osmocom/openpcd/hardware/RFID-READER_Bm115_1.pdf

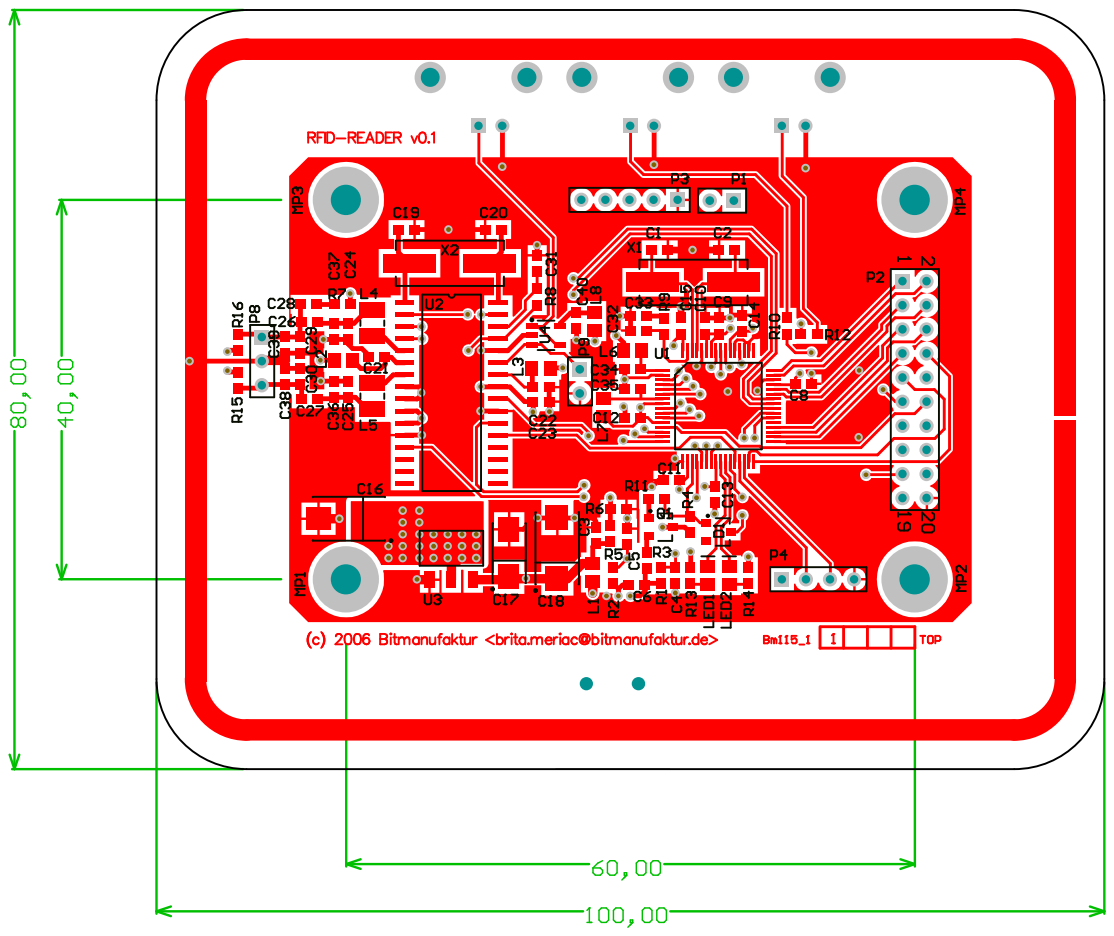
[picture p21: page 1]

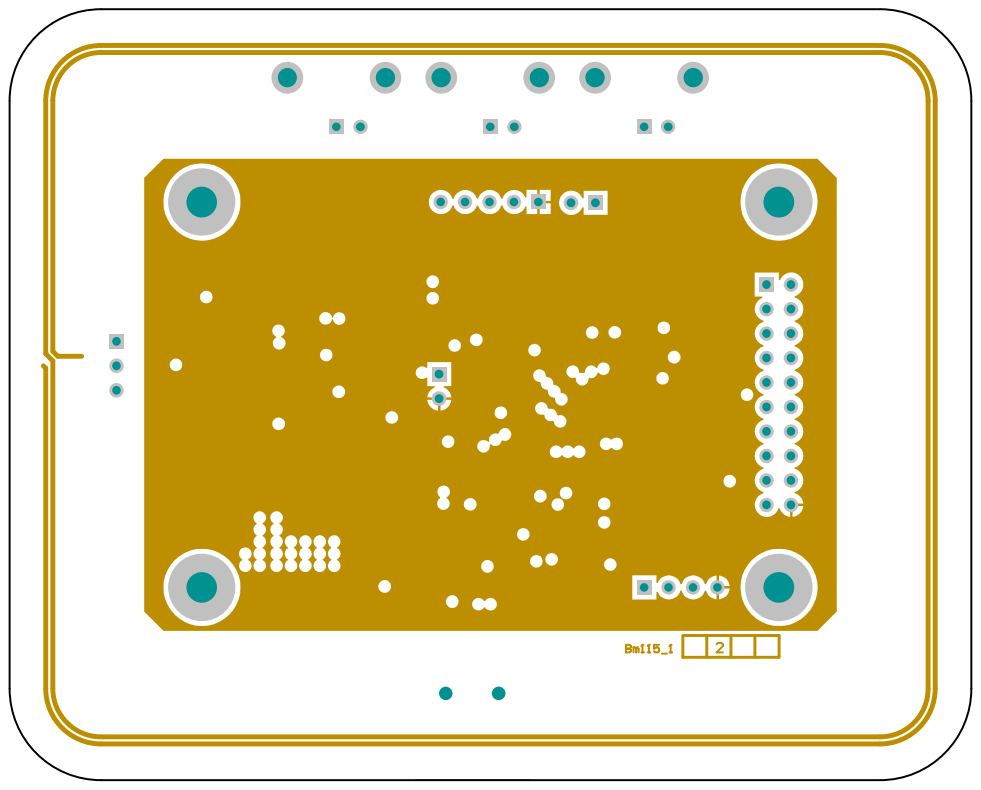
[picture p22: page 2]

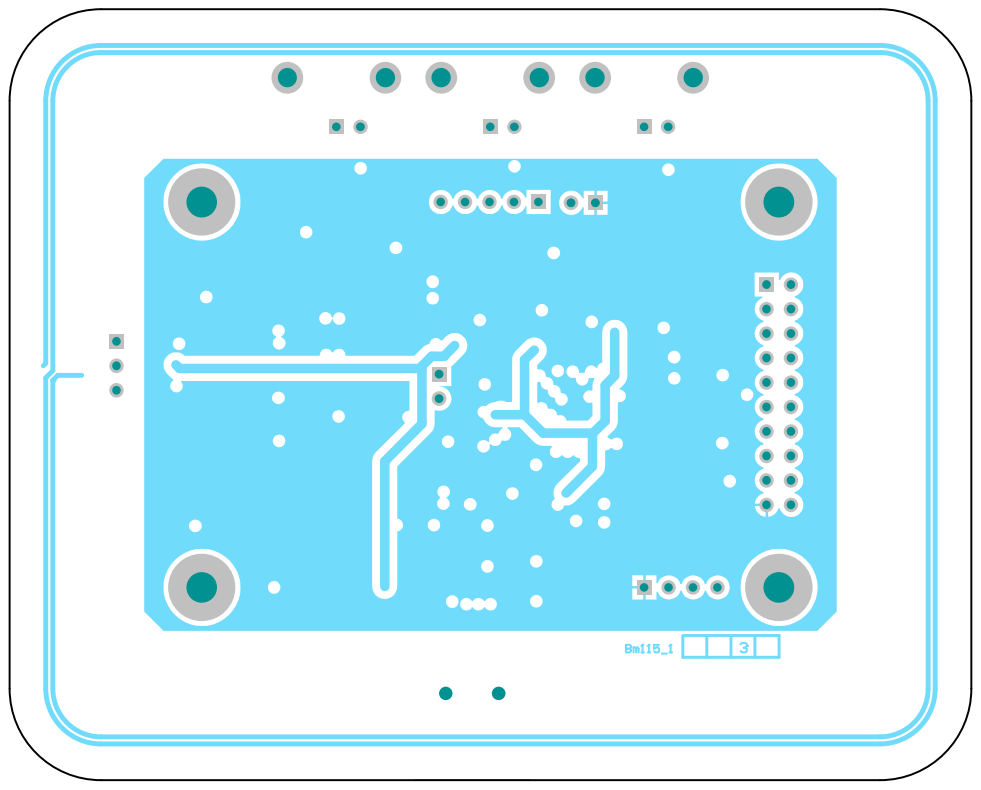
[picture p23: page 3]

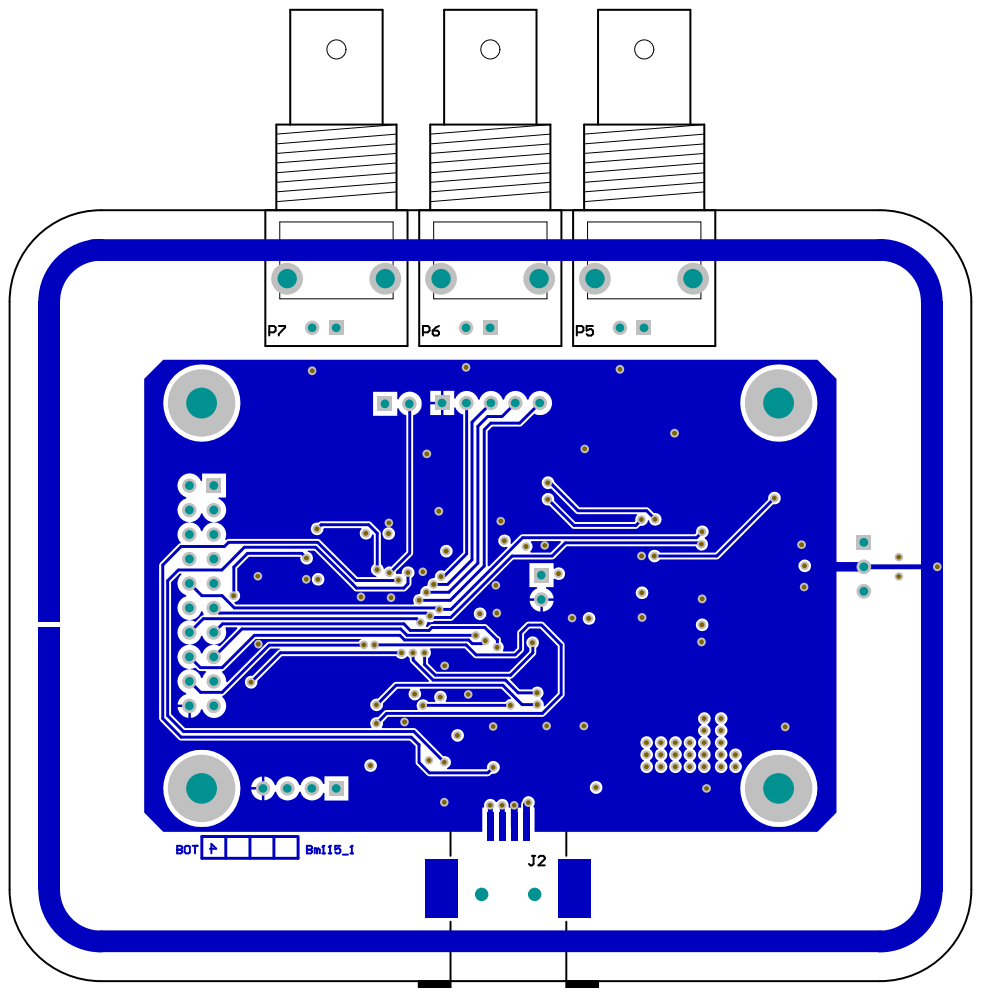
[picture p24: page 4]

Date:; Sheet of File:; H:\Projekte\..\TOP.SchDoc; Drawn By; 1 - TOP

Title
Testboard RFID Reader

http://www.bitmanufaktur.de

Dipl.-Ing. Brita Meriac

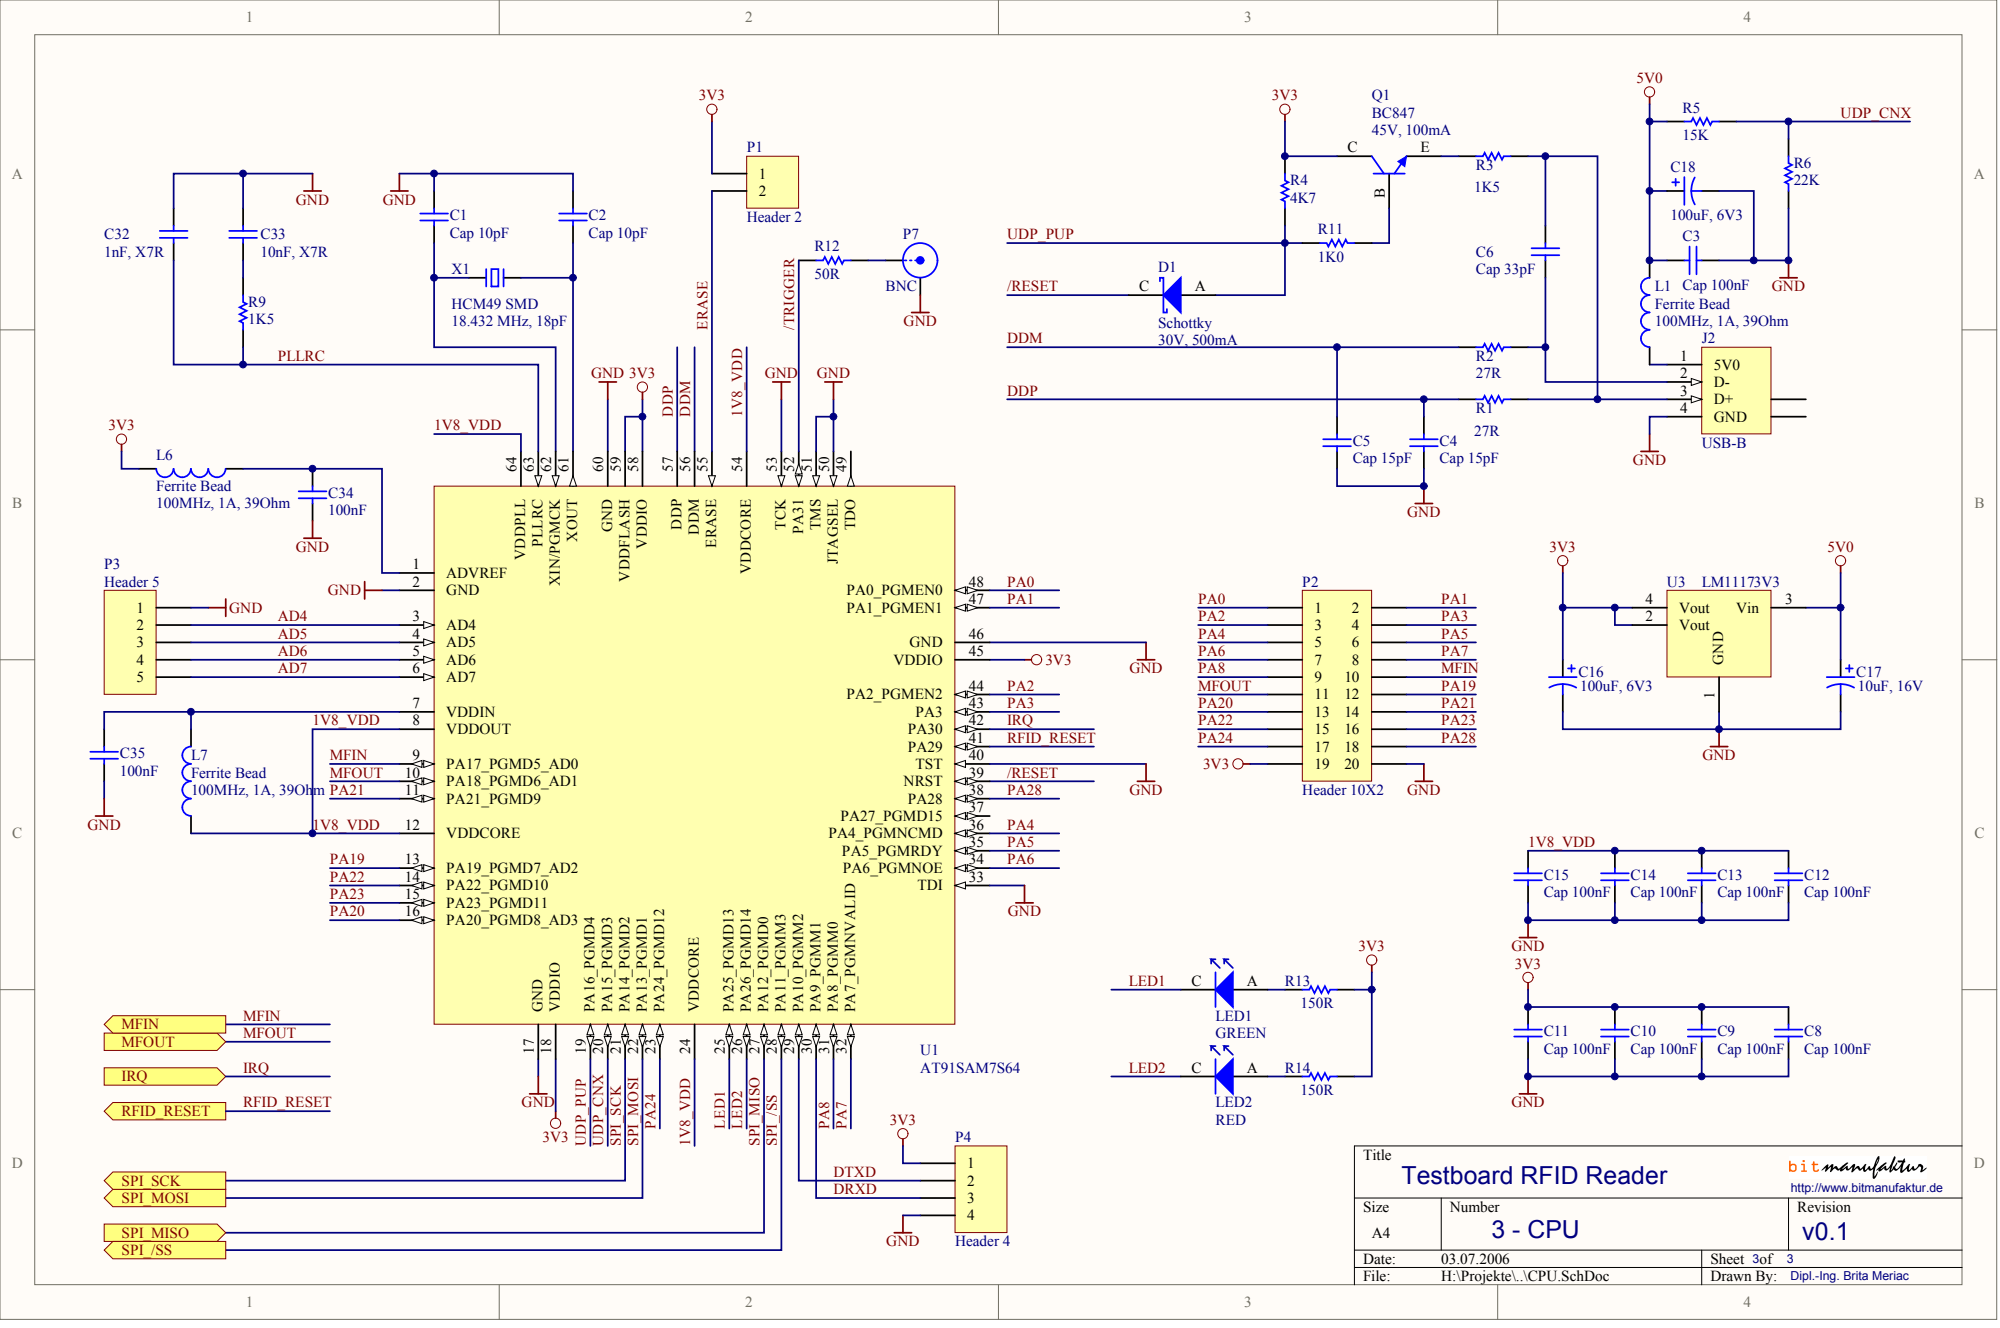
[picture p25: page 6]

18.432 MHz, 18pF 1V8_VDD N01V80VDD N01V80VDD

XOUT 61 XIN/PGMCK 62 PLLRC 63 VDDPLL 64

1V8_VDD N01V80VDD | 8

MF IN N0MFIN MFOUT N0MFOUT N0PA21 1V8_VDD N01V80VDD | 9 | PA18_PGMD6_AD1 10 PA21_PGMD9 11 P0U1011 N0PA21

DTXD N0DTXD N0DTXD
DRXD N0DRXD N0DRXD | P0P402 P0P402

http://www.bitmanufaktur.de

Dipl.-Ing. Brita Meriac

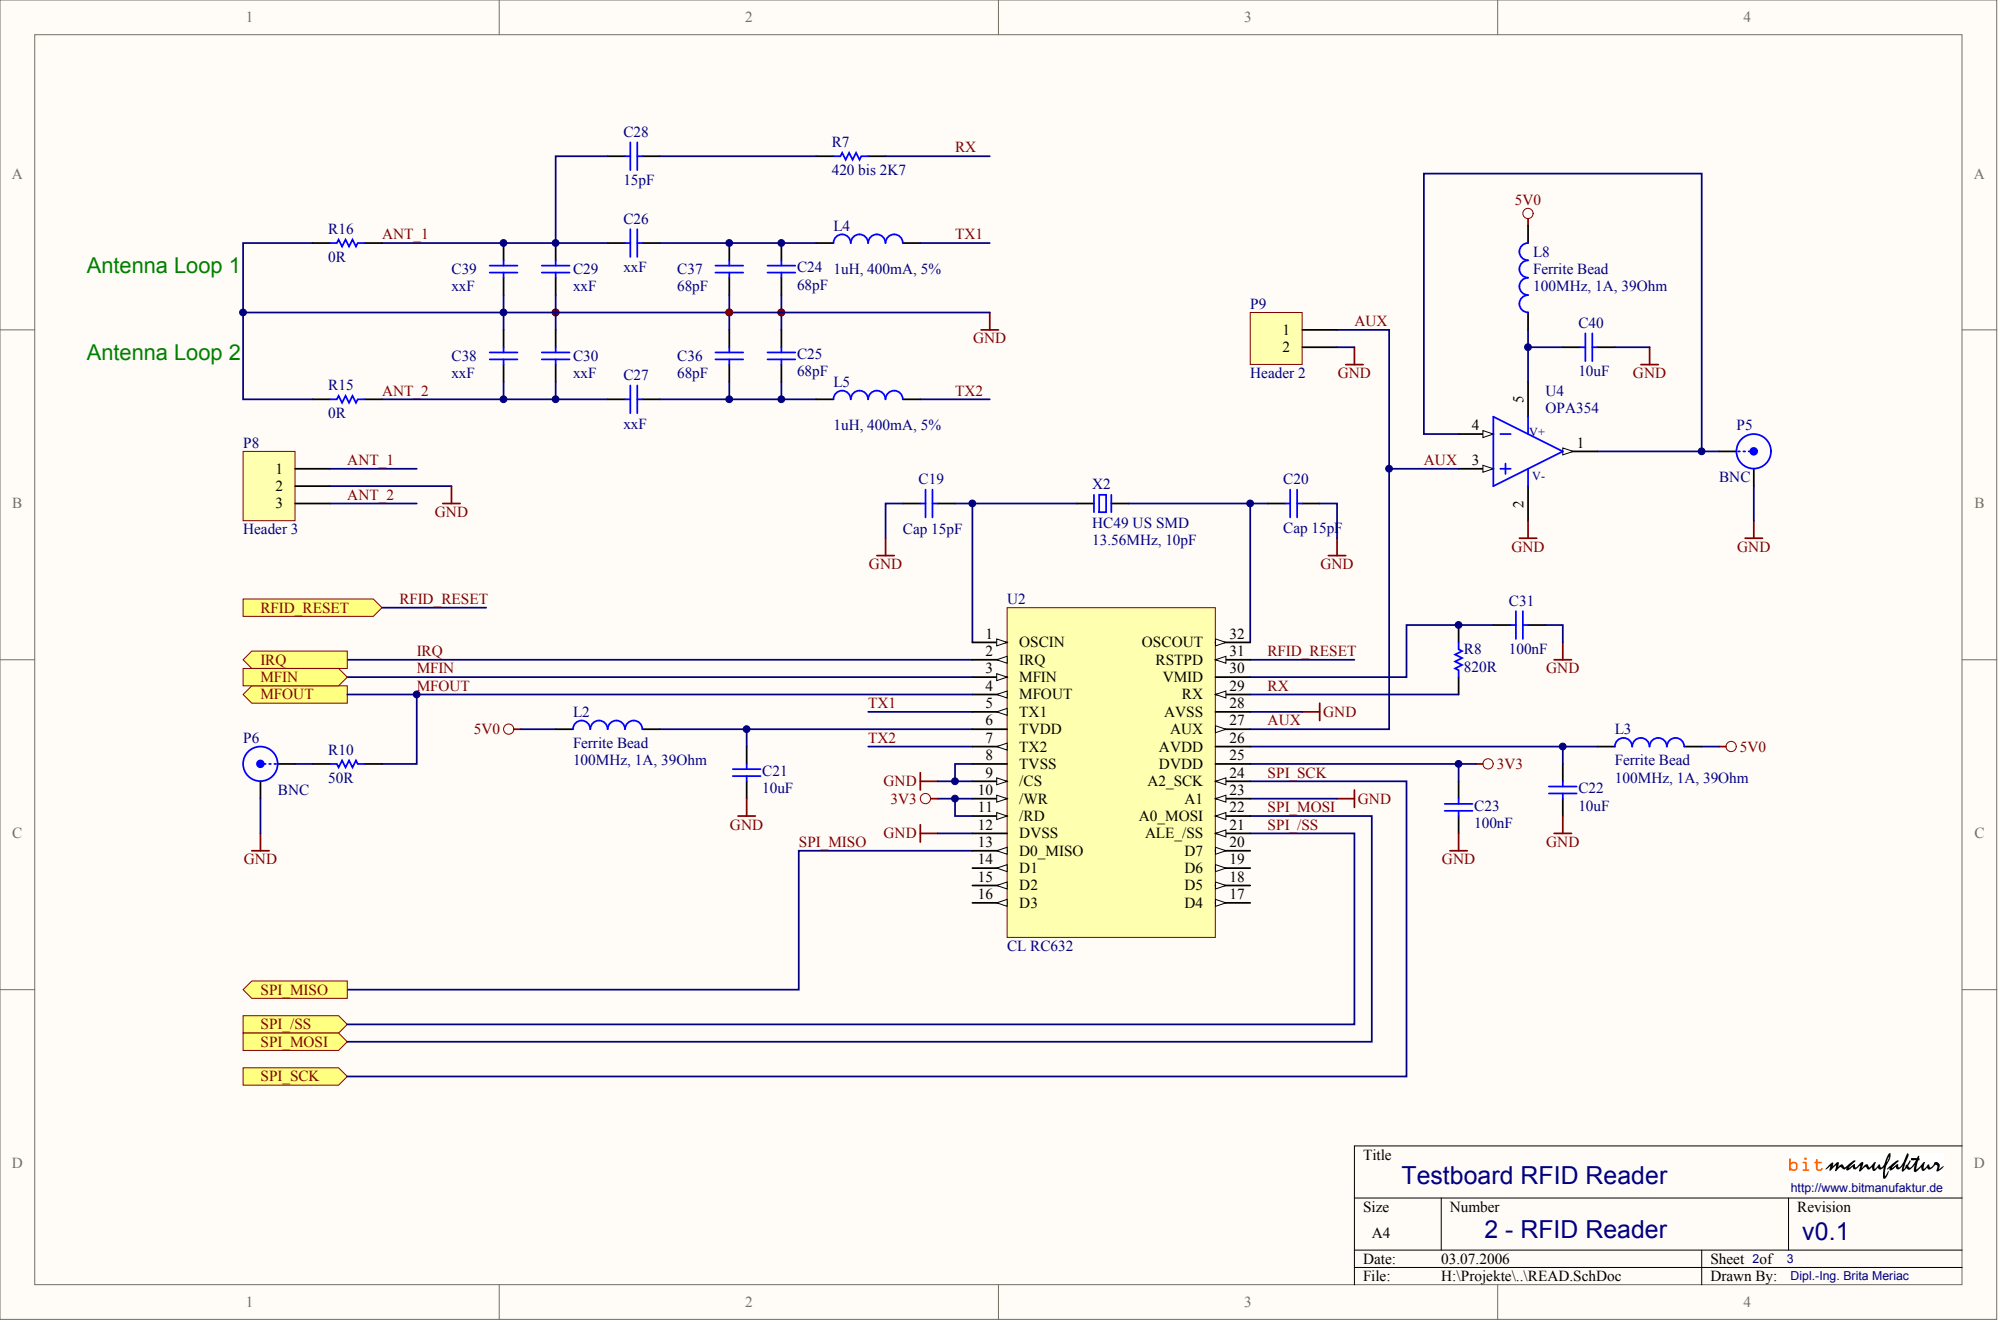
[picture p26: page 7]

RFID_RESET N0RFID0RESET | R8

MFOUT 4 P0U204 N0MFOUT P0U2029 P0U2029 P0U2029 P0U2029 | RX N0RX

TX1 5 P0U2028 P0U2028 P0U2028 P0U2028 TVDD 6 TX2 7 TVSS 8 /CS 9

P0U2010 P0U2010 | /WR 10
/RD 11 | SPI_MOSI
DVSS 12 P0U2021 P0U2021 P0U2021 P0U2021 | SPI_/SS N0SPI0/SS

SPI_MISO | D0_MISO 13 P0U2013 N0SPI0MISO P0U2020 P0U2020 P0U2020 P0U2020 P0U2013 P0U2013 P0U2013

D1 14 P0U2019 P0U2019 P0U2019 P0U2019
D2 15 P0U2018 P0U2018 P0U2018 P0U2018

http://www.bitmanufaktur.de

Dipl.-Ing. Brita Meriac
