osmocom/openpcd/hardware/RFID-READER_SCH01.pdf

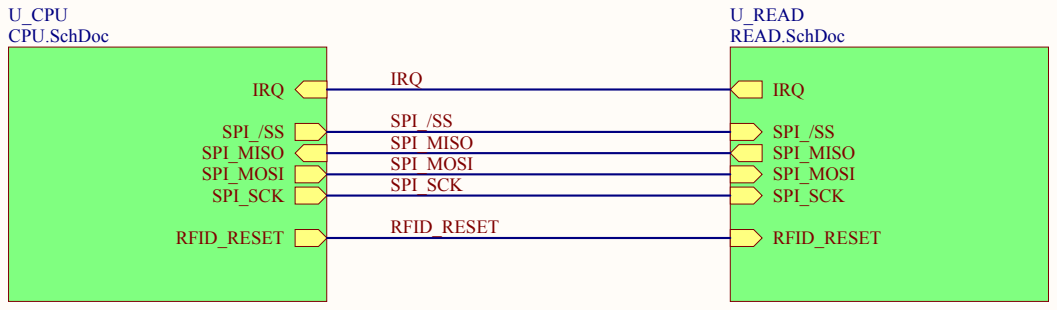
[picture p27: page 1]
Date:; Sheet of; File:; H:\Projekte\..\TOP.SchDoc; Drawn By:; 1 - TOP

Title
Testboard RFID Reader

http://www.bitmanufaktur.de

Dipl.-Ing. Brita Meriac

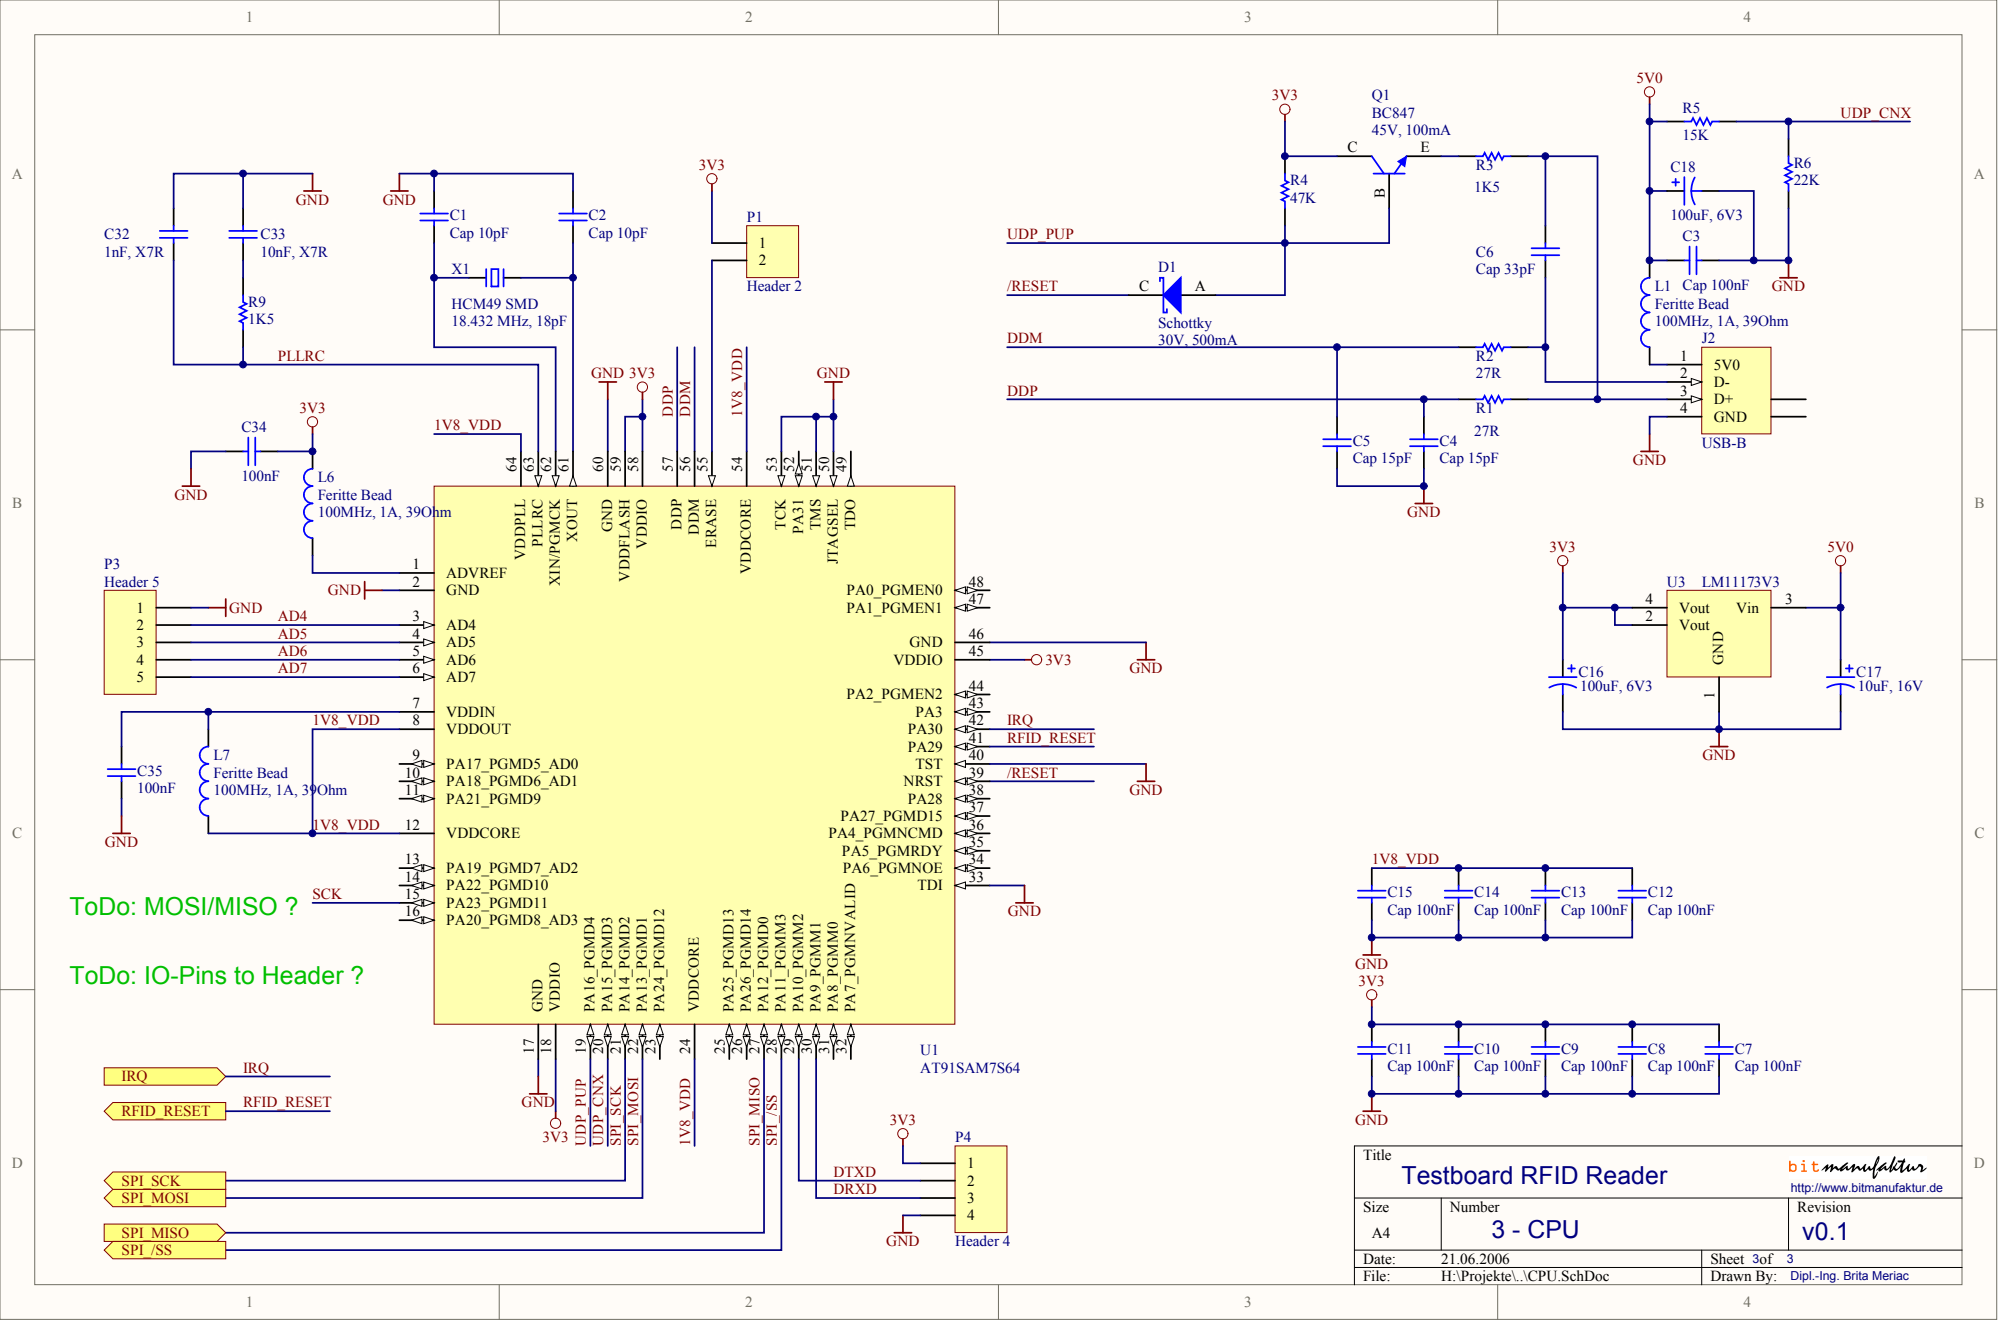
[picture p28: page 2]

18.432 MHz, 18pF 1V8_VDD N01V80VDD N01V80VDD

XOUT 61 XIN/PGMCK 62 PLLRC 63 VDDPLL 64

1V8_VDD N01V80VDD | 8

1V8_VDD N01V80VDD | 9

ToDo: IO-Pins to Header ?

http://www.bitmanufaktur.de

Dipl.-Ing. Brita Meriac

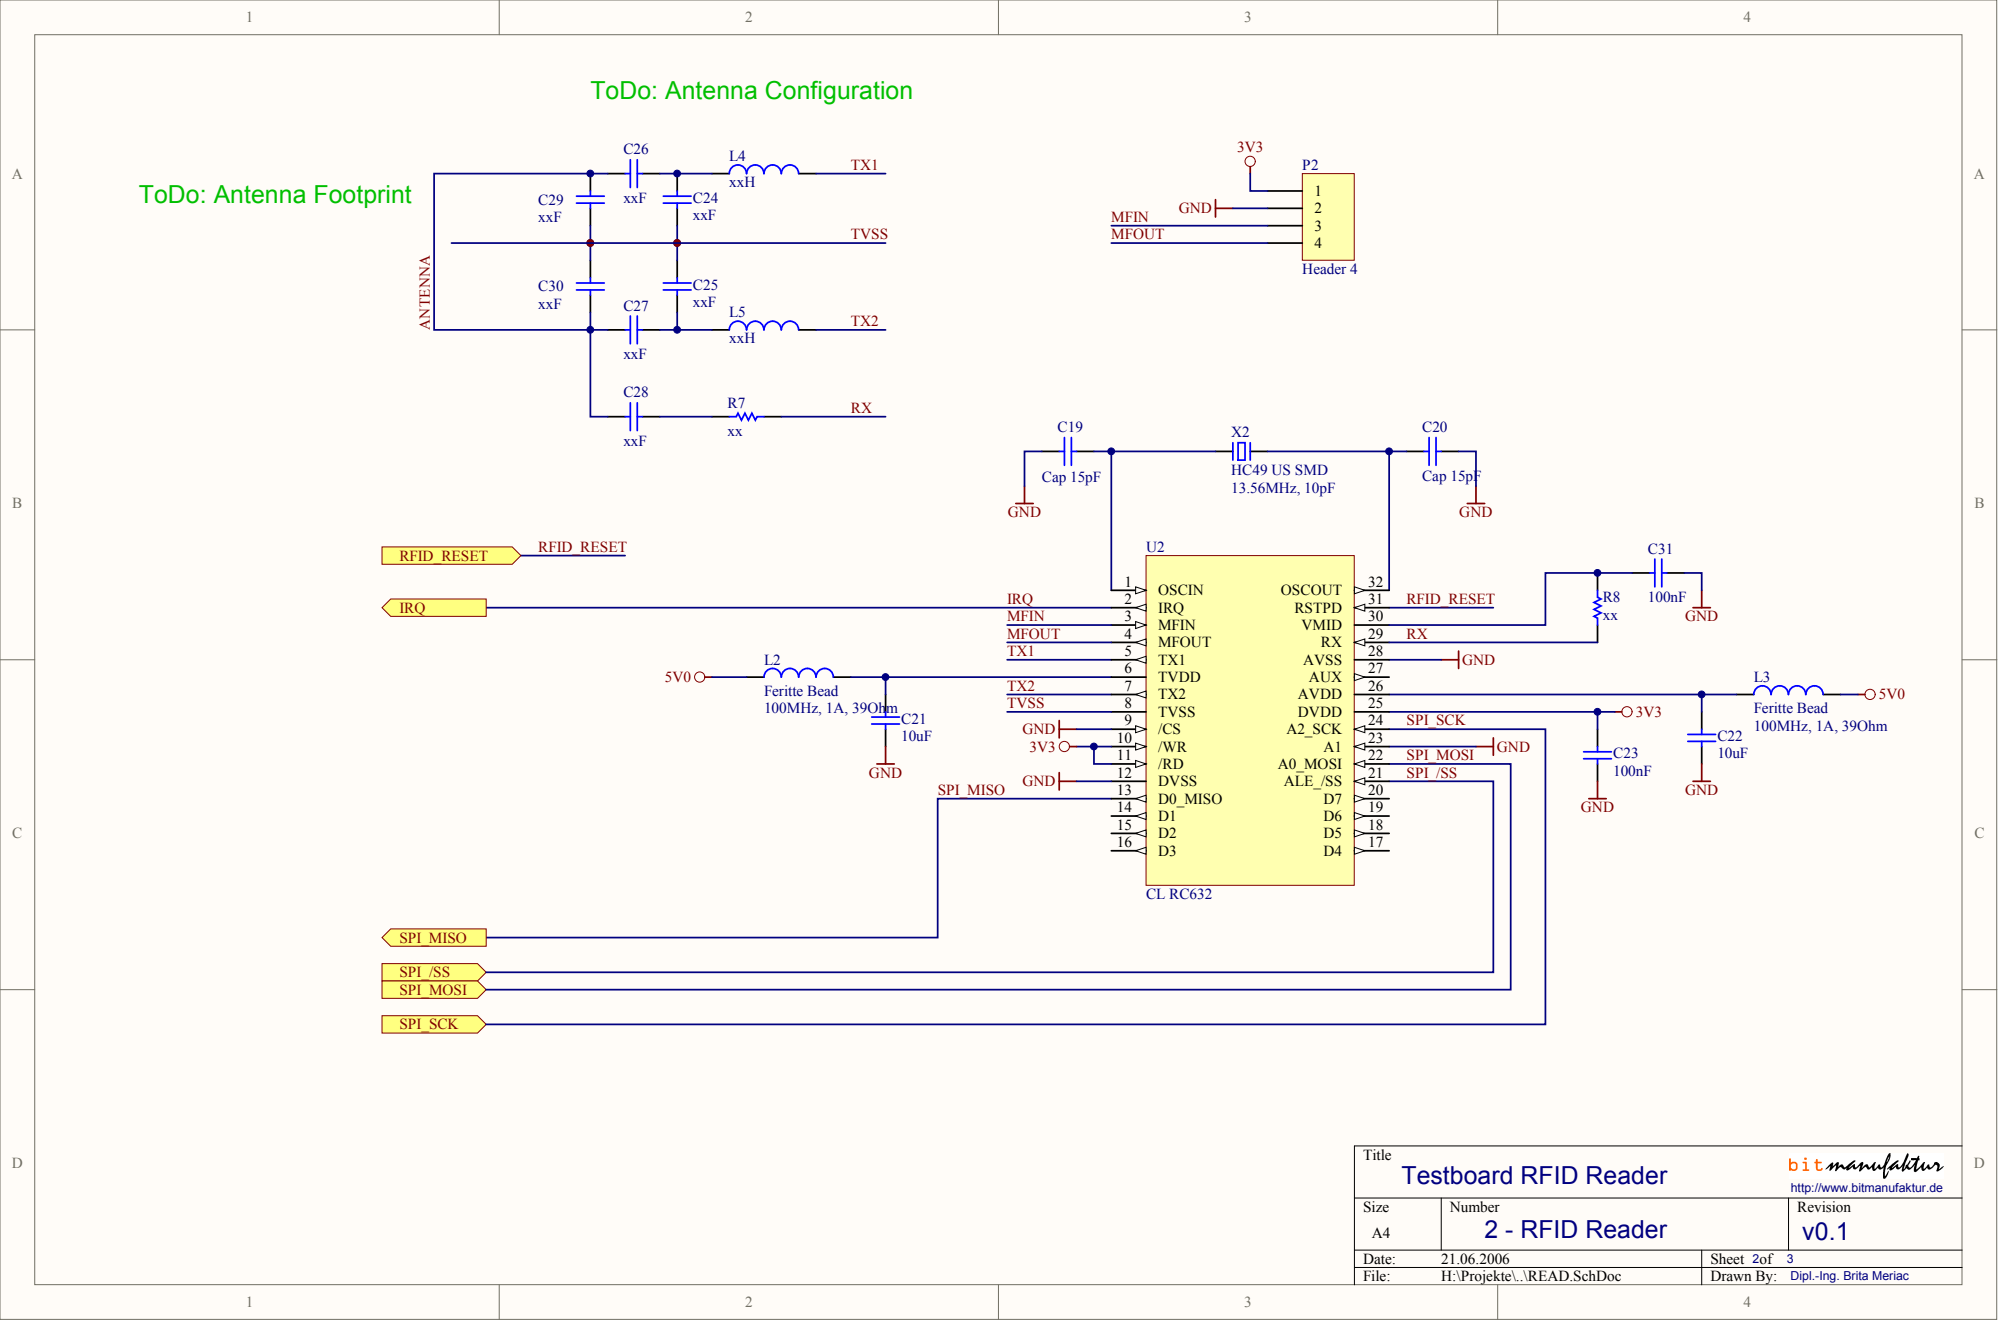
[picture p29: page 3]

P0U2010 P0U2010 | /WR 10 P0U2022 P0U2022 P0U2022
/RD 11 | SPI_MOSI
DVSS 12 P0U2021 P0U2021 P0U2021 P0U2021 | SPI_/SS N0SPI0/SS

SPI_MISO | D0_MISO 13 P0U2013 N0SPI0MISO P0U2020 P0U2020 P0U2020 P0U2020 P0U2013 P0U2013 P0U2013

D1 14 P0U2019 P0U2019 P0U2019 P0U2019
D2 15 P0U2018 P0U2018 P0U2018 P0U2018

http://www.bitmanufaktur.de

Dipl.-Ing. Brita Meriac
