osmocom/openpcd/hardware/v0.4/openpcd_v04-pcb.pdf

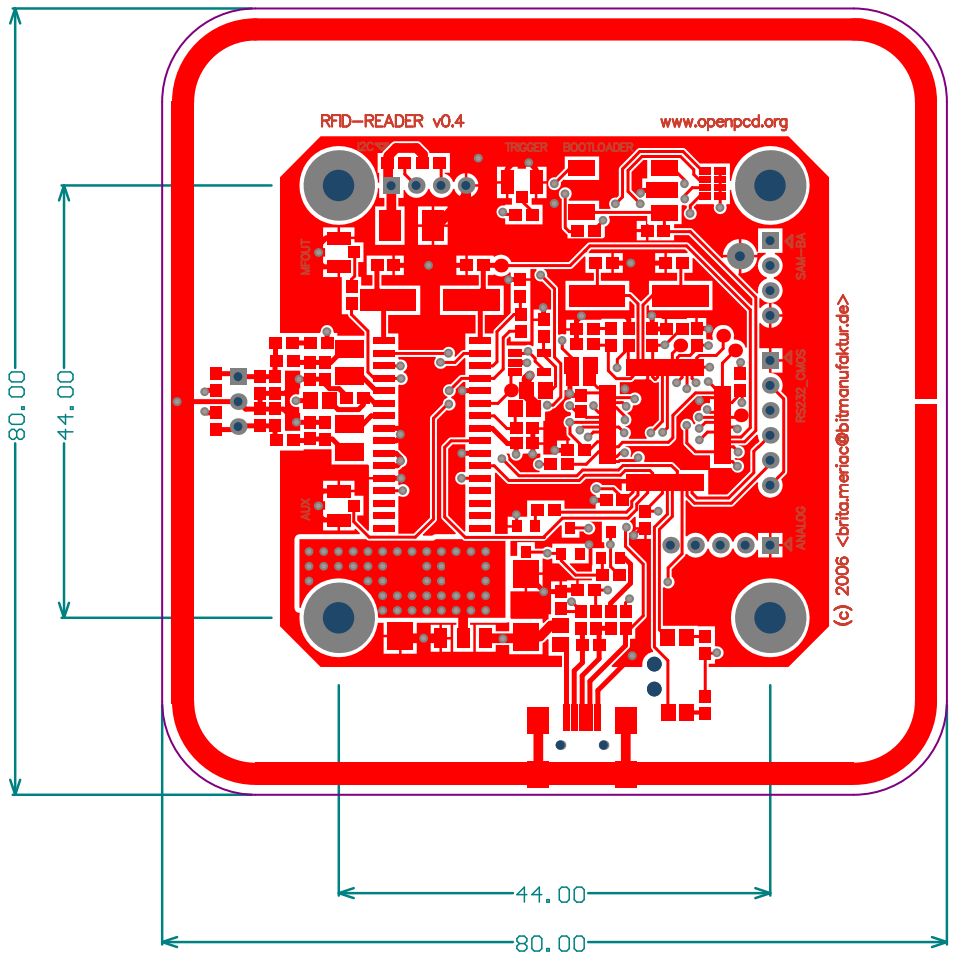
[picture p30: page 1]

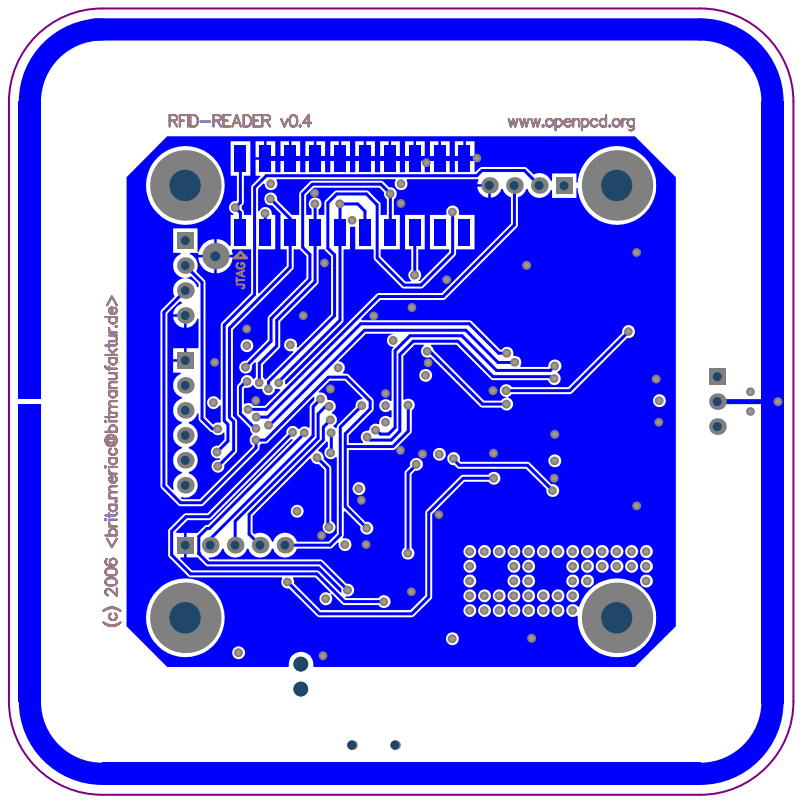
[picture p31: page 2]

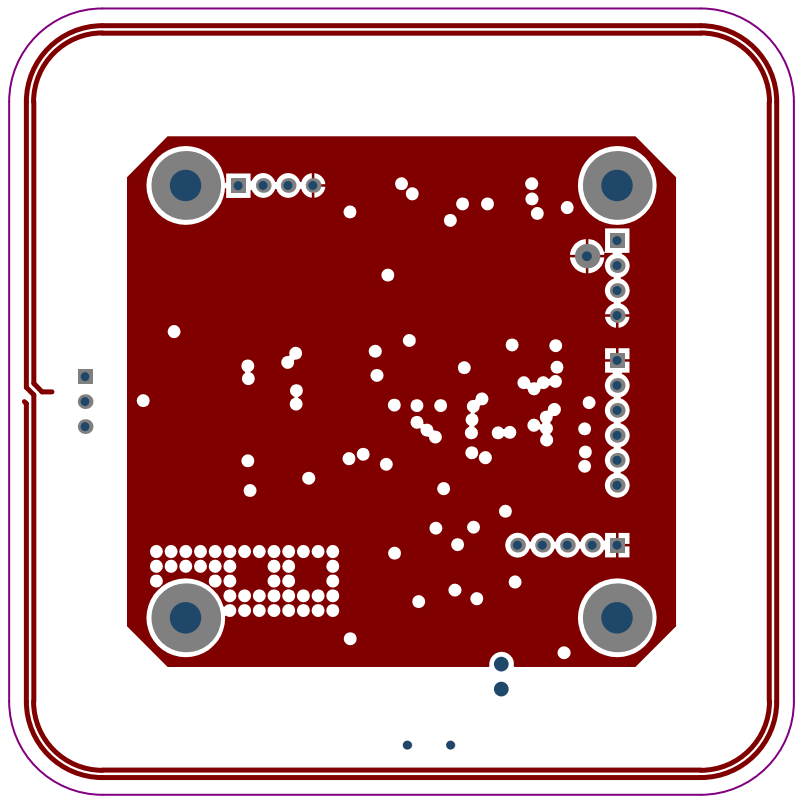
[picture p32: page 3]

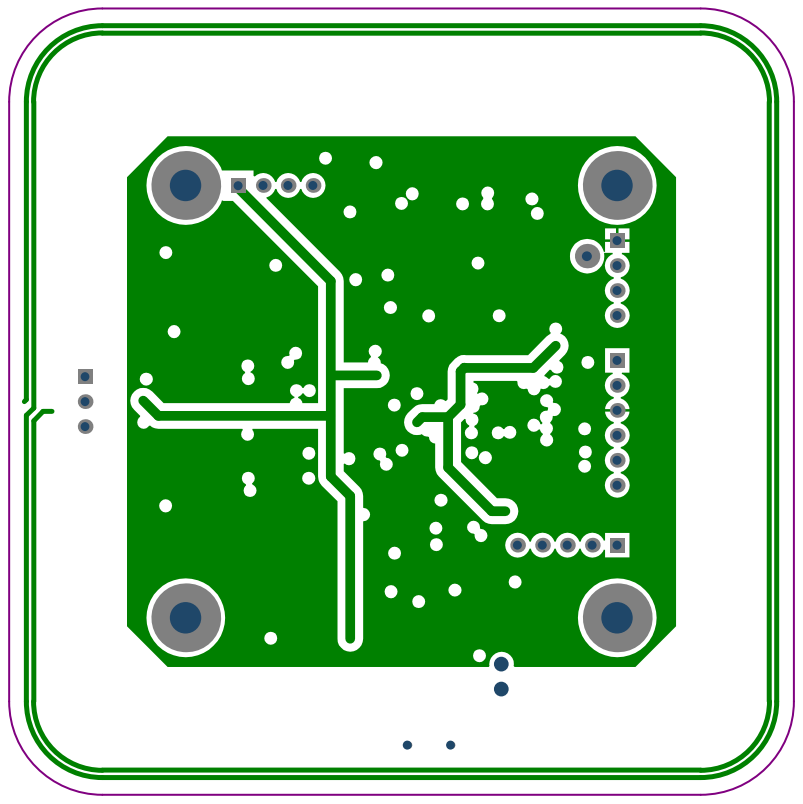
[picture p33: page 4]
