osmocom/openpcd/hardware/v0.4/openpcd_v04-sch.pdf

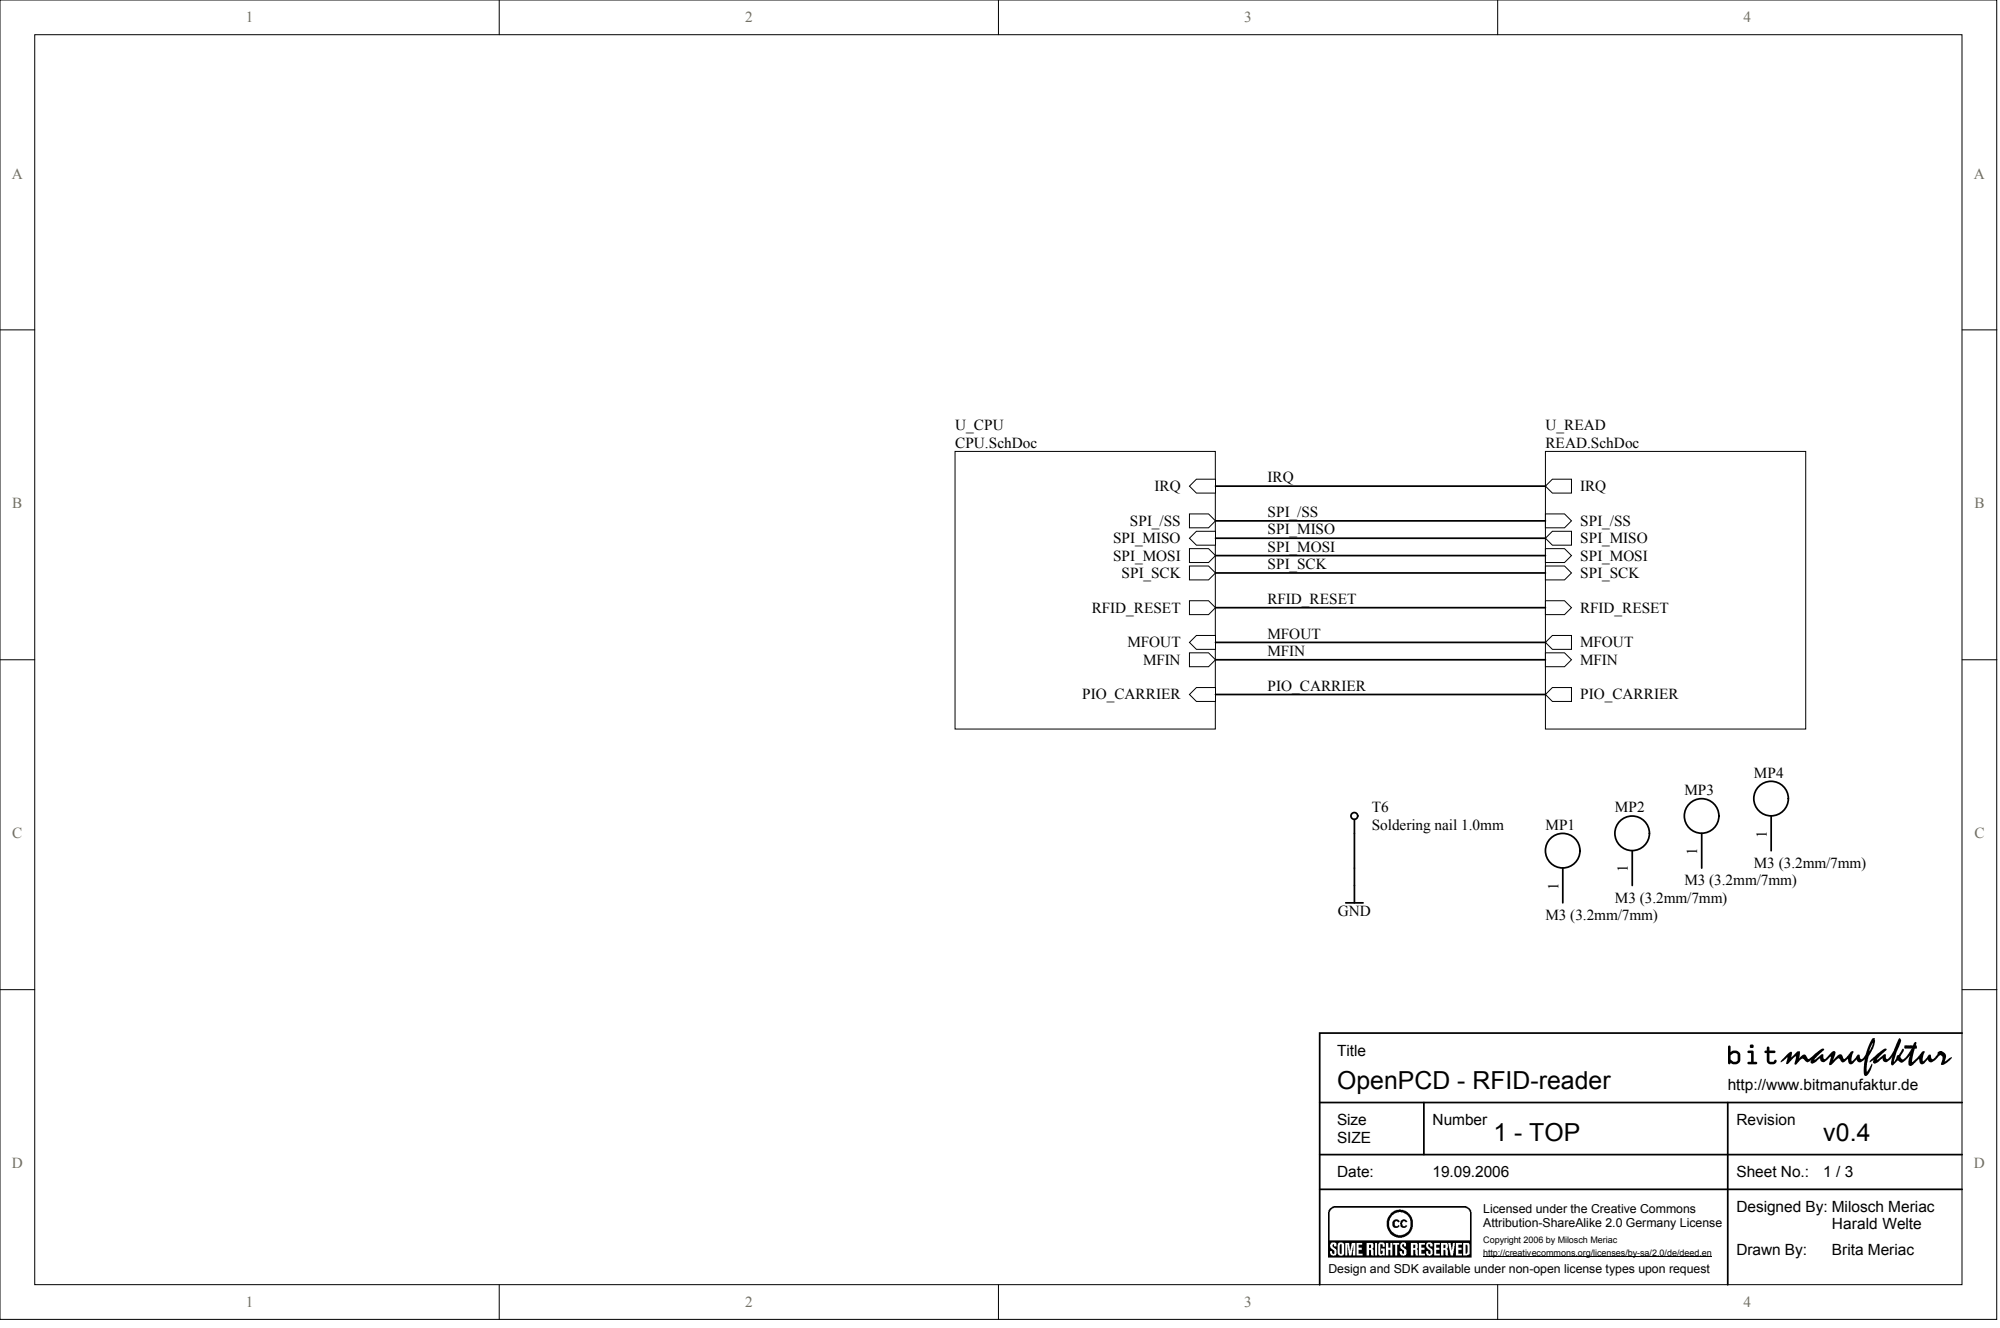
[picture p34: page 1]
Soldering nail 1.0m; Design and SDK available under non-open license types upon request P0MP101

Title
OpenPCD - RFID-reader

ww.bitmanufaktur.de

Siz e SIZE | Number 1 - TOP | Revision v0.4

Date: 19.09.2006 | | Sheet No.: 1 / 3

Licensed under the Creative Commons Attribution-ShareAlike 2.0 Germany License http://creativecommons.org/licenses/by-sa/2.0/de/deed.en Cop yri g ht 2006 b y Mi losch Meriac | | Designed By : Milosch Meriac Harald Welte Drawn By : Brita Meriac

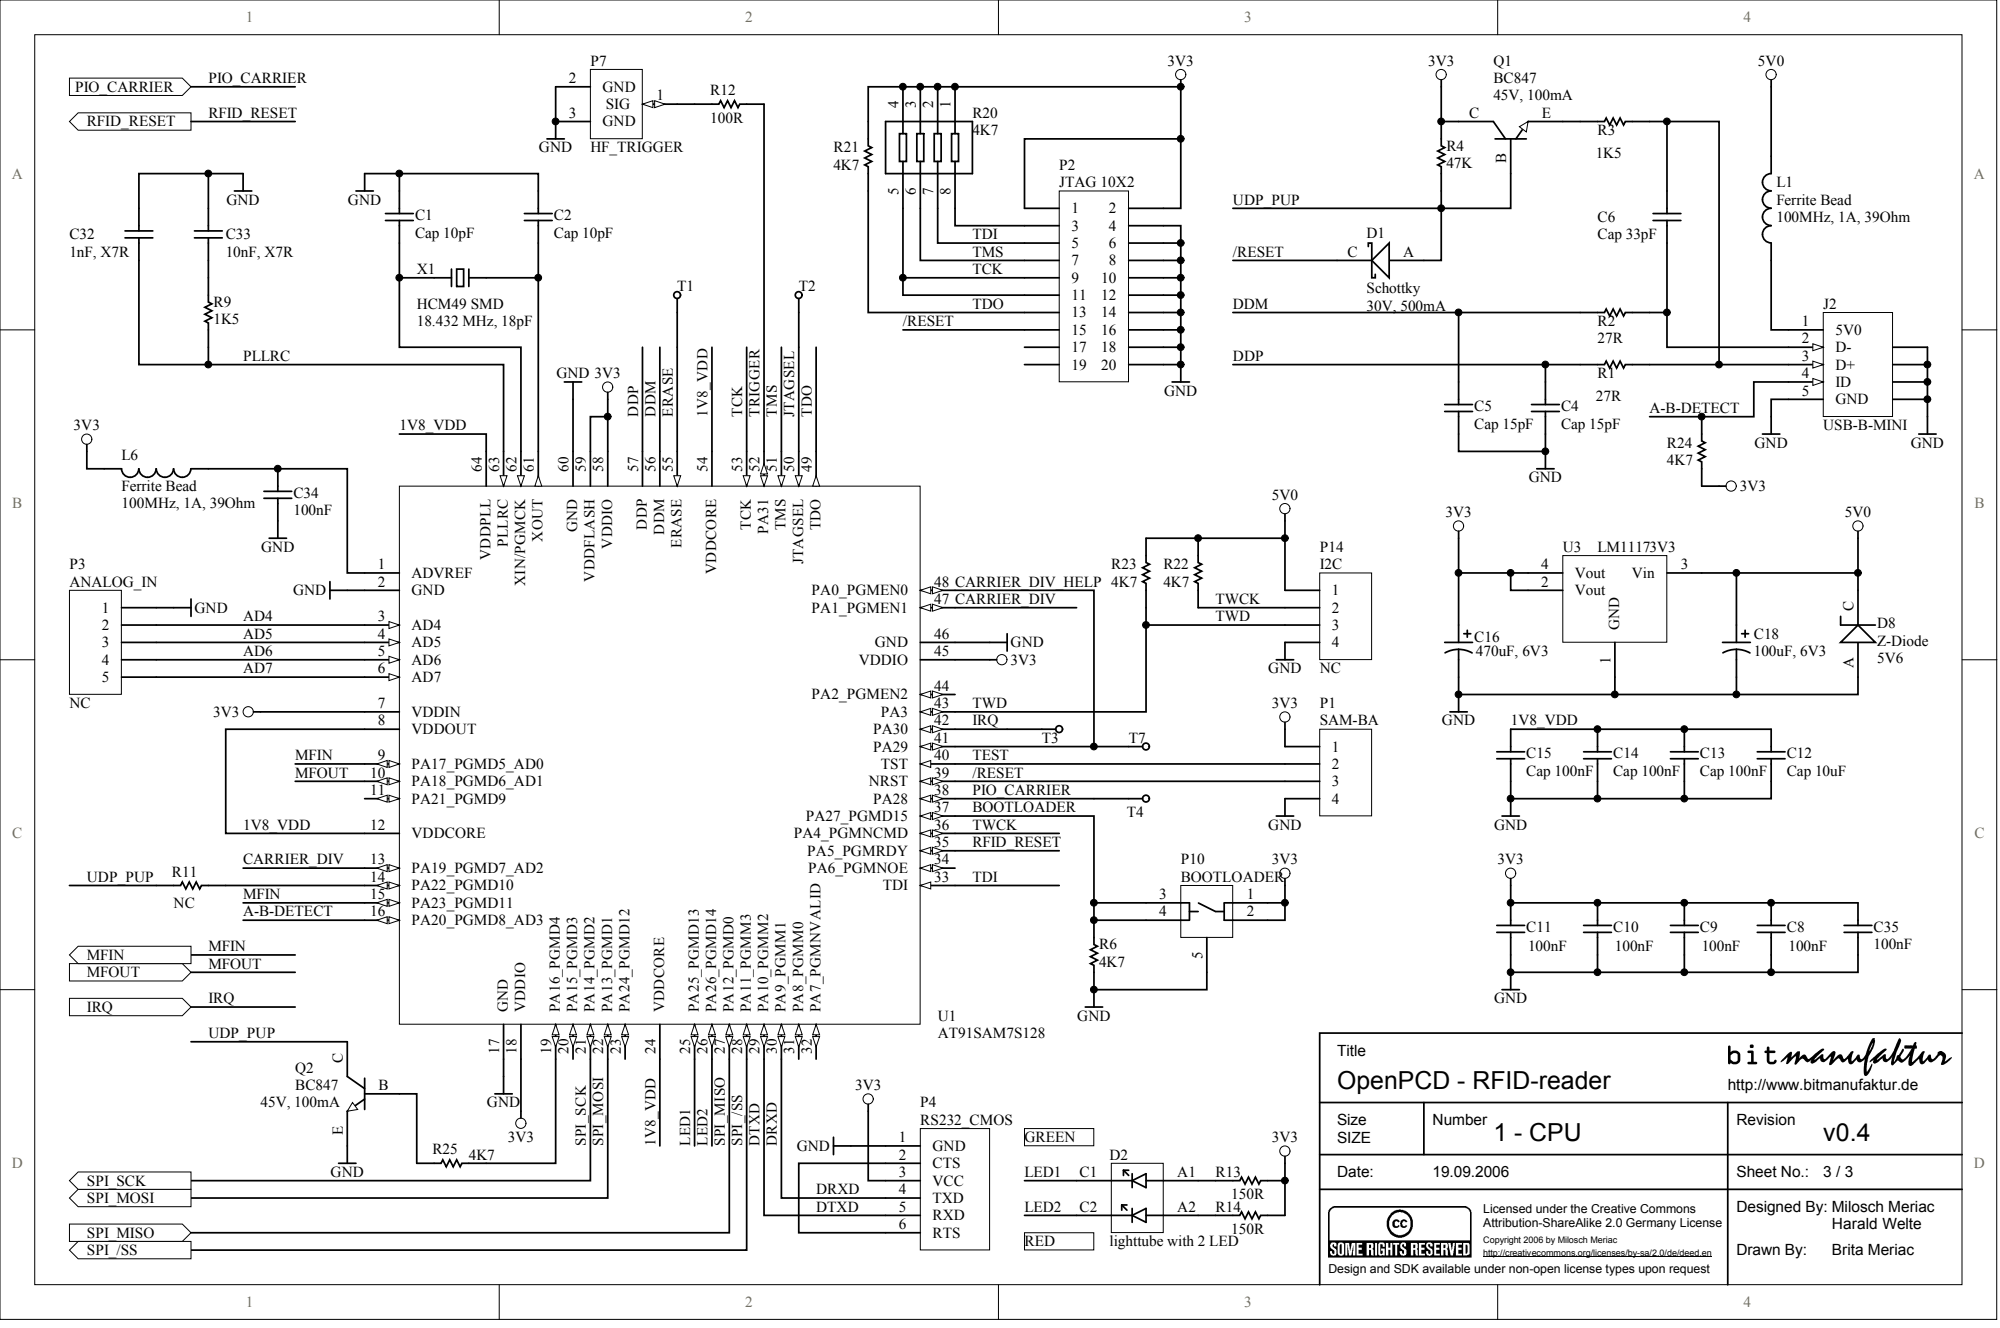
[picture p35: page 2]

XOUT 61 XIN/PGMCK 62 PLLRC 63 VDDPLL 64

Siz e SIZE | Number 1 - CPU | Revision v0.4

4 | | LED1 LED2 C2 N0LED2 | P0R1302 P0R1302 P0R1302 P0R1302 P0R1301 P0R1301 P0R1301 P0R1301 A2 R14 P0D20A2 P0D20A2 P0D20A2 P0D20A2

Date: 19.09.2006 | | Sheet No.: 3 / 3

DTXD N0DTXD | 5

Licensed under the Creative Commons Attribution-ShareAlike 2.0 Germany License http://creativecommons.org/licenses/by-sa/2.0/de/deed.en Cop yri g ht 2006 b y Mi losch Meriac Design and SDK available under non-open license types upon request | | Designed By : Milosch Meriac Harald Welte Drawn By : Brita Meriac

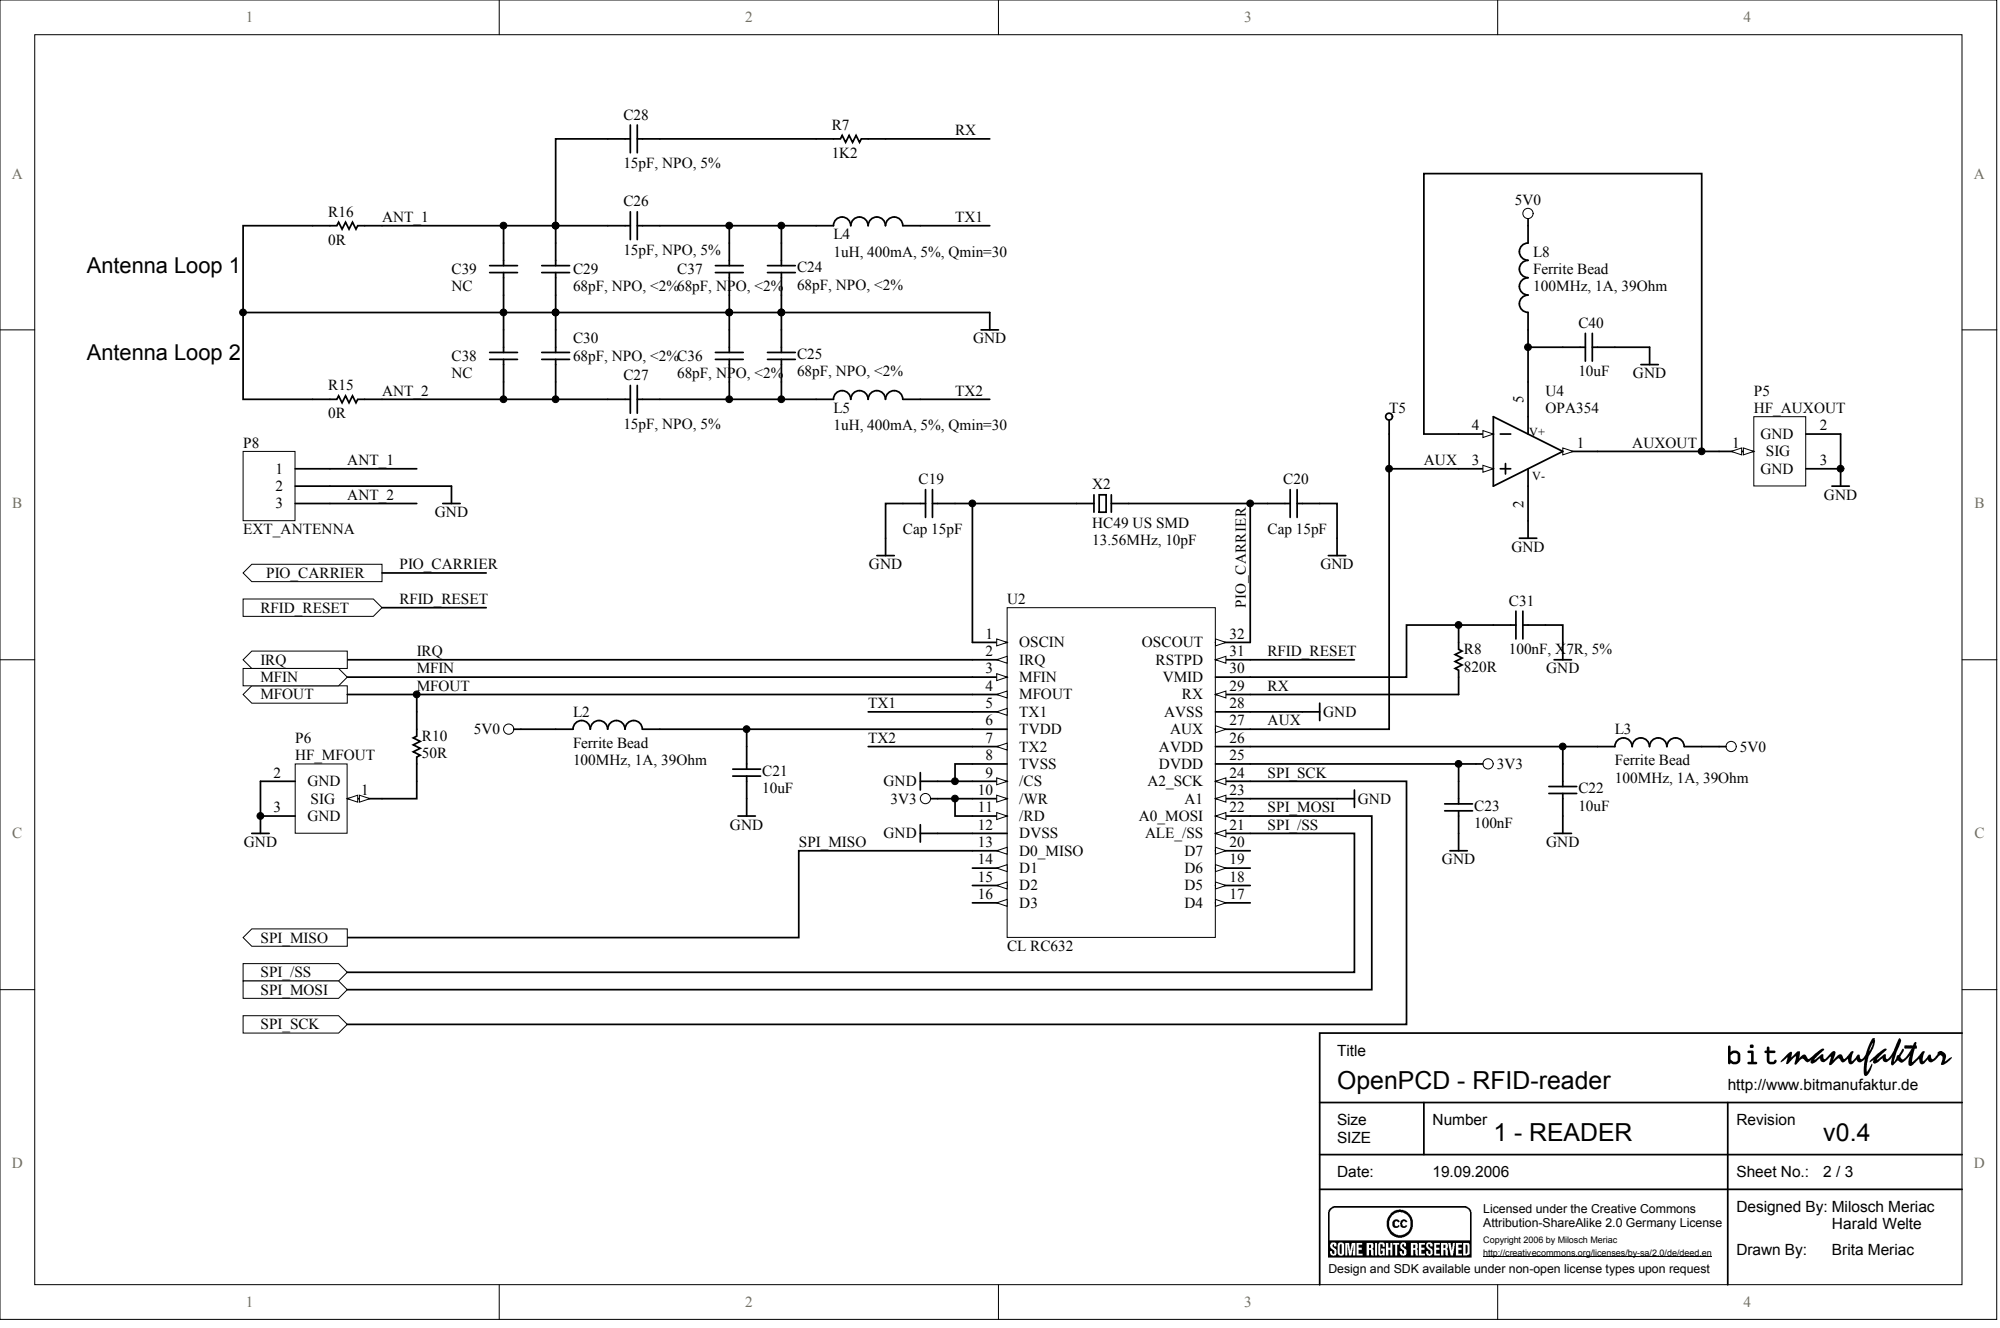
[picture p36: page 3]

RF ID_RESET N0RFID0RESET | R8

P0U204 N0MFOUT P0U2029 P0U2029 P0U2029 P0U2029 | | RX N0RX

3 | P0P601 P0P601 | 1 GND | | P0U2010 P0U2010 | /WR 10

/RD 11 | SP I_MOSI
DVSS 12 P0U2021 P0U2021 P0U2021 P0U2021 | SP I_/SS N0SPI0/SS

SP I_MISO | D0_MISO 13 P0U2013 N0SPI0MISO P0U2020 P0U2020 P0U2020 P0U2020 P0U2013 P0U2013 P0U2013

D1 14 P0U2019 P0U2019 P0U2019 P0U2019
D2 15 P0U2018 P0U2018 P0U2018 P0U2018

Siz e SIZE | Number 1 - READER | Revision v0.4

Date: 19.09.2006 | | Sheet No.: 2 / 3

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
