osmocom/openpcd/hardware/v0.4/openpcd_v04_place.pdf

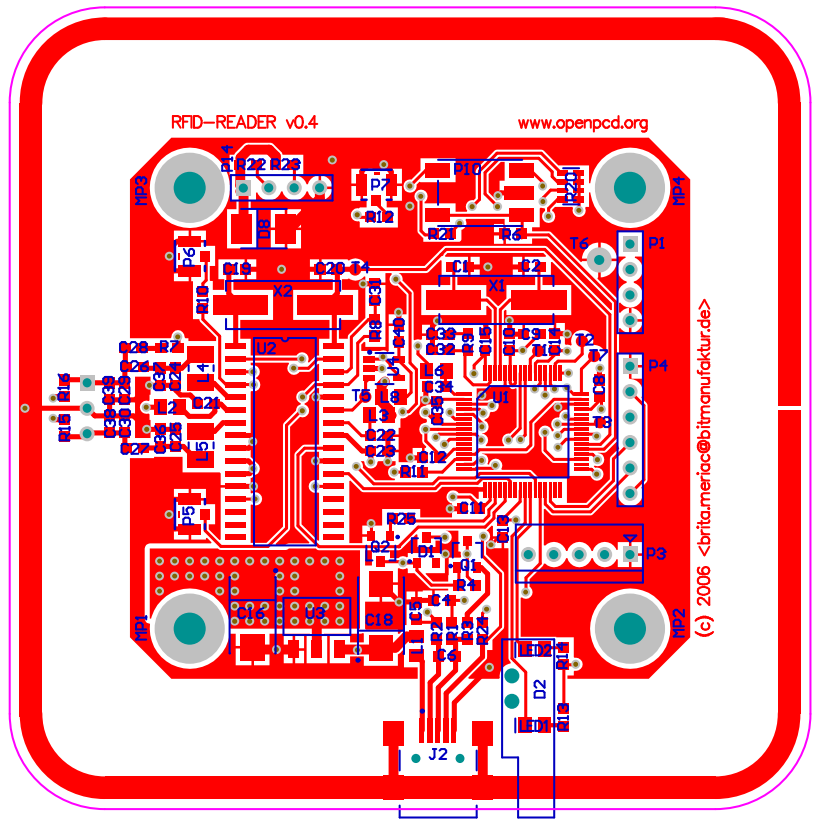
[picture p37: page 1]
