osmocom/openpcd/openpicc/application/ssc.c

/* AT91SAM7 SSC controller routines for OpenPICC
 * (C) 2006 by Harald Welte <hwelte@hmw-consulting.de>
 * (C) 2007-2008 Henryk Plötz <henryk@ploetzli.ch>
 *
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
 * We use SSC for both TX and RX side.
 *
 * RX side is interconnected with demodulated carrier 
 *
 * TX side is interconnected with load modulation circuitry
 */

#include <FreeRTOS.h>
#include <queue.h>
#include <task.h>
#include <openpicc.h>

#include <string.h>
#include <errno.h>

#include "ssc.h"
#include "iso14443.h"

#include "clock_switch.h"
#include "tc_cdiv_sync.h"
#include "tc_fdt.h"
#include "led.h"

#include "usb_print.h"
#include "cmd.h"

#define PRINT_DEBUG 0
#define DEBUG_DATA_GATING 0

struct _ssc_handle {
	enum ssc_mode mode;
	const struct openpicc_hardware *openpicc;
	ssc_dma_rx_buffer_t* rx_buffer[2];
	ssc_dma_tx_buffer_t* tx_buffer;
	ssc_callback_t callback;
	xQueueHandle rx_queue;
	AT91PS_PDC pdc;
	AT91PS_SSC ssc;
	u_int8_t rx_enabled, tx_enabled;
	u_int8_t rx_running, tx_running, tx_need_switching;
};

static ssc_handle_t _ssc;
static const ssc_mode_def ssc_modes[] = {
	/* Undefined, no size set */
	[SSC_MODE_NONE]		   = {SSC_MODE_NONE, 0, 0, 0},
	/* 14443A Frame */
	[SSC_MODE_14443A]      = {SSC_MODE_14443A, 
		ISO14443_BITS_PER_SSC_TRANSFER * ISO14443A_SAMPLE_LEN,               // transfersize_ssc 
		ISO14443_BITS_PER_SSC_TRANSFER * ISO14443A_SAMPLE_LEN <= 8 ? 8 : 16, // transfersize_pdc 
		DIV_ROUND_UP(ISO14443A_MAX_RX_FRAME_SIZE_IN_BITS, ISO14443_BITS_PER_SSC_TRANSFER) },
};
static struct {
	ssc_metric metric;
	char *name;
	int value;
} ssc_metrics[] = {
		[METRIC_RX_OVERFLOWS]      = {METRIC_RX_OVERFLOWS, "Rx overflows", 0},
		[METRIC_FREE_RX_BUFFERS]   = {METRIC_FREE_RX_BUFFERS, "Free Rx buffers", 0},
		[METRIC_MANAGEMENT_ERRORS] = {METRIC_MANAGEMENT_ERRORS, "Internal buffer management error", 0},
		[METRIC_MANAGEMENT_ERRORS_1] = {METRIC_MANAGEMENT_ERRORS_1, "Internal buffer management error type 1", 0},
		[METRIC_MANAGEMENT_ERRORS_2] = {METRIC_MANAGEMENT_ERRORS_2, "Internal buffer management error type 2", 0},
		[METRIC_MANAGEMENT_ERRORS_3] = {METRIC_MANAGEMENT_ERRORS_3, "Internal buffer management error type 3", 0},
		[METRIC_LATE_TX_FRAMES]    = {METRIC_LATE_TX_FRAMES, "Late Tx frames", 0},
		[METRIC_RX_FRAMES]         = {METRIC_RX_FRAMES, "Rx frames", 0},
		[METRIC_TX_FRAMES]         = {METRIC_TX_FRAMES, "Tx frames", 0},
		[METRIC_TX_ABORTED_FRAMES] = {METRIC_TX_ABORTED_FRAMES, "Aborted Tx frames", 0},
};

static ssc_dma_rx_buffer_t _rx_buffers[SSC_DMA_BUFFER_COUNT];
ssc_dma_tx_buffer_t        _tx_buffer;

/******* PRIVATE "meat" code *************************************************/

#define SSC_RX_IRQ_MASK	(AT91C_SSC_RXRDY | 	\
			 AT91C_SSC_OVRUN | 	\
			 AT91C_SSC_ENDRX |	\
			 AT91C_SSC_RXBUFF |	\
			 AT91C_SSC_RXSYN |	\
			 AT91C_SSC_CP0 |	\
			 AT91C_SSC_CP1)

#define SSC_TX_IRQ_MASK (AT91C_SSC_TXRDY |	\
			 AT91C_SSC_TXEMPTY | 	\
			 AT91C_SSC_ENDTX |	\
			 AT91C_SSC_TXBUFE |	\
			 AT91C_SSC_TXSYN)

static __ramfunc ssc_dma_rx_buffer_t* _unload_rx(ssc_handle_t *sh);
static __ramfunc int _reload_rx(ssc_handle_t *sh);


static int __ramfunc _ssc_rx_irq(u_int32_t orig_sr, int start_asserted, portBASE_TYPE task_woken)
{
	int end_asserted = 0;
	ssc_handle_t *sh = &_ssc;
	u_int32_t orig_rcmr = sh->ssc->SSC_RCMR;
	
#if PRINT_DEBUG
	int old = usb_print_set_default_flush(0);  // DEBUG OUTPUT
	DumpStringToUSB("orig:");  // DEBUG OUTPUT
	DumpUIntToUSB(orig_sr);  // DEBUG OUTPUT
	DumpStringToUSB("\n\r");  // DEBUG OUTPUT
#endif
	u_int32_t sr = orig_sr | _ssc.ssc->SSC_SR;
	
	if( (sr & AT91C_SSC_RXSYN) || start_asserted) {
		sh->ssc->SSC_RCMR = (orig_rcmr & (~AT91C_SSC_START)) | (AT91C_SSC_START_CONTINOUS);
		/* Receiving has started */
		if(sh->callback != NULL) {
			sh->callback(SSC_CALLBACK_RX_FRAME_BEGIN, &end_asserted);
			if(end_asserted)
				sr = orig_sr | _ssc.ssc->SSC_SR;
		}
	}
	
#if PRINT_DEBUG	
	DumpStringToUSB("sr:");  // DEBUG OUTPUT
	DumpUIntToUSB(sr);  // DEBUG OUTPUT
	DumpStringToUSB("\n\r");  // DEBUG OUTPUT
	usb_print_set_default_flush(old);  // DEBUG OUTPUT
#endif
	
	if(((sr & (AT91C_SSC_CP1 | AT91C_SSC_ENDRX)) || end_asserted) && (sh->rx_buffer[0] != NULL)) {
		/* Receiving has ended */
		AT91F_PDC_DisableRx(sh->pdc);
		AT91F_SSC_DisableRx(sh->ssc);
		sh->ssc->SSC_RCMR = ((sh->ssc->SSC_RCMR) & (~AT91C_SSC_START)) | (AT91C_SSC_START_0);

		ssc_dma_rx_buffer_t *buffer = _unload_rx(sh);
		if(buffer != NULL) {
			if(sh->callback != NULL)
				sh->callback(SSC_CALLBACK_RX_FRAME_ENDED, buffer);

			if(buffer->state != SSC_FREE) {
				task_woken = xQueueSendFromISR(sh->rx_queue, &buffer, task_woken);
			}
		}
		
		if(_reload_rx(sh)) {
			/* Clear the receive holding register. Is this necessary? */
			int dummy = sh->ssc->SSC_RHR; (void)dummy;
			AT91F_PDC_EnableRx(sh->pdc);
			if(!sh->tx_running) {
				/* Only start the receiver if no Tx has been started. Warning: Need
				 * to make sure that the receiver is restarted again when the Tx is over.
				 * Note that this is only necessary when not using Compare 0 to start
				 * reception. When using Compare 0 the data gating mechanism will keep
				 * CP0 from happening and thus keep the receiver stopped.
				 *
				 * Note also that we're not resetting rx_running to 0, because conceptionally
				 * the Rx is still running,. So rx_running=1 and tx_running=1 means SSC_RX
				 * stopped and SSC_RX should be started as soon as SSC_TX stops.
				 */
				AT91F_SSC_EnableRx(sh->ssc);
			}
		} else {
			sh->ssc->SSC_IDR = SSC_RX_IRQ_MASK;
			sh->rx_running = 0;
			sh->callback(SSC_CALLBACK_RX_STOPPED, sh);
		}
		
	}

	sh->ssc->SSC_RCMR = orig_rcmr;
	return task_woken;
}

/* Exported callback for the case when the frame start has been detected externally */
void ssc_frame_started(void)
{
	_ssc_rx_irq(_ssc.ssc->SSC_SR, 1, pdFALSE);
}

static void __ramfunc _ssc_tx_end(ssc_handle_t *sh, int is_an_abort)
{
	AT91F_PDC_DisableTx(sh->pdc);
	AT91F_SSC_DisableTx(sh->ssc);
	sh->ssc->SSC_IDR = SSC_TX_IRQ_MASK;
	
	AT91F_PIO_CfgPeriph(AT91C_BASE_PIOA, AT91C_PA15_TF, 0);
	usb_print_string_f(">",0);
	
	AT91F_PDC_SetTx(sh->pdc, 0, 0);
	AT91F_PDC_SetNextTx(sh->pdc, 0, 0);

	if(sh->tx_buffer) {
		sh->tx_buffer->state = SSC_FREE;
		sh->tx_running = 0;
	}
	
	if(sh->rx_running) {
		/* Receiver has been suspended by the pending transmission. Restart it. */
		AT91F_SSC_EnableRx(sh->ssc);
	}
	
	if(sh->callback) {
		if(is_an_abort)
			sh->callback(SSC_CALLBACK_TX_FRAME_ABORTED, sh->tx_buffer);
		else
			sh->callback(SSC_CALLBACK_TX_FRAME_ENDED, sh->tx_buffer);
	}
		
	sh->tx_buffer = NULL;
}

static int __ramfunc _ssc_tx_irq(u_int32_t sr, portBASE_TYPE task_woken)
{
	ssc_handle_t *sh = &_ssc;
	
	if( sr & AT91C_SSC_TXSYN ) {
		/* Tx starting, hardwire TF pin to high */
		AT91F_PIO_SetOutput(AT91C_BASE_PIOA, AT91C_PA15_TF);
		AT91F_PIO_CfgOutput(AT91C_BASE_PIOA, AT91C_PA15_TF);
		usb_print_string_f("<",0);
		
		/* Also set SSC mode to continous 
		 * FIXME BUG: This will somehow add two samples on the SSC 
		 * The abomination below is designed to find a pause in the outgoing modulation data
		 * (WARNING: Will only work with manchester, not with PSK) so that the SSC start type
		 * switch will happen during a time of no subcarrier modulation (in order to not
		 * upset the subcarrier). Still need to find a way to 'absorb' the extra two samples. */
		if(sh->tx_need_switching) {
			vLedSetGreen(0);
			int j = 0;
off_pre:
			if(j++ > 100) goto out;
			if(!AT91F_PIO_IsInputSet(AT91C_BASE_PIOA, OPENPICC_MOD_PWM)) {
				goto off_pre;
			}
on:
			if(j++ > 100) goto out;
			if(AT91F_PIO_IsInputSet(AT91C_BASE_PIOA, OPENPICC_MOD_PWM)) goto on;
			int i=0;
off:
			if(j++ > 100) goto out;
			if(!AT91F_PIO_IsInputSet(AT91C_BASE_PIOA, OPENPICC_MOD_PWM)) {
				if(i++ > 2) goto out; else goto off;
			} else goto on;
out:
			sh->ssc->SSC_TCMR = (sh->ssc->SSC_TCMR & ~AT91C_SSC_START) | AT91C_SSC_START_CONTINOUS;
			vLedSetGreen(1);
		}

		if(sh->callback) 
			sh->callback(SSC_CALLBACK_TX_FRAME_BEGIN, NULL);
	}
	
	if( sr & AT91C_SSC_TXEMPTY ) {
		/* Tx has ended */
		ssc_metrics[METRIC_TX_FRAMES].value++;
		_ssc_tx_end(sh, 0);
	}
	
	return task_woken;
}

static void __ramfunc ssc_irq(void) __attribute__ ((naked));
static void __ramfunc ssc_irq(void)
{
	portENTER_SWITCHING_ISR();
	vLedSetRed(1);
	portBASE_TYPE task_woken = pdFALSE;
	
	u_int32_t sr = _ssc.ssc->SSC_SR;
	if(sr & AT91C_SSC_RXSYN) {
		task_woken = _ssc_rx_irq(sr, 1, task_woken);
	} else if(sr & SSC_RX_IRQ_MASK) {
		task_woken = _ssc_rx_irq(sr, 0, task_woken);
	}
	
	if(sr & SSC_TX_IRQ_MASK) {
		task_woken = _ssc_tx_irq(sr, task_woken);
	}
	
	AT91F_AIC_ClearIt(AT91C_ID_SSC);
	AT91F_AIC_AcknowledgeIt();

	vLedSetRed(0);
	portEXIT_SWITCHING_ISR(task_woken);
}

static __ramfunc ssc_dma_rx_buffer_t *_get_buffer(ssc_dma_buffer_state_t old, ssc_dma_buffer_state_t new)
{
	ssc_dma_rx_buffer_t *buffer = NULL;
	int i;
	for(i=0; i < SSC_DMA_BUFFER_COUNT; i++) {
		if(_rx_buffers[i].state == old) {
			buffer = &_rx_buffers[i];
			buffer->state = new;
			break;
		}
	}
	return buffer;
}

/* Doesn't check sh, must be called with interrupts disabled */
static __ramfunc int _reload_rx(ssc_handle_t *sh)
{
	int result = 0;
	if(sh->rx_buffer[0] != NULL) {
		ssc_metrics[METRIC_MANAGEMENT_ERRORS_1].value++;
		result = 1;
		goto out;
	}
	
	ssc_dma_rx_buffer_t *buffer = _get_buffer(SSC_FREE, SSC_PENDING);
	
	if(buffer == NULL) {
		ssc_metrics[METRIC_RX_OVERFLOWS].value++;
		goto out;
	}

	buffer->reception_mode = &ssc_modes[sh->mode];
	buffer->len_transfers = ssc_modes[sh->mode].transfers;
	
	AT91F_PDC_SetRx(sh->pdc, buffer->data, buffer->len_transfers);
	sh->rx_buffer[0] = buffer;
	
	result = 1;
out:
	return result;
}
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
